eduarbo/filo36/docs/images/branding/flan36-caramel-drop.png

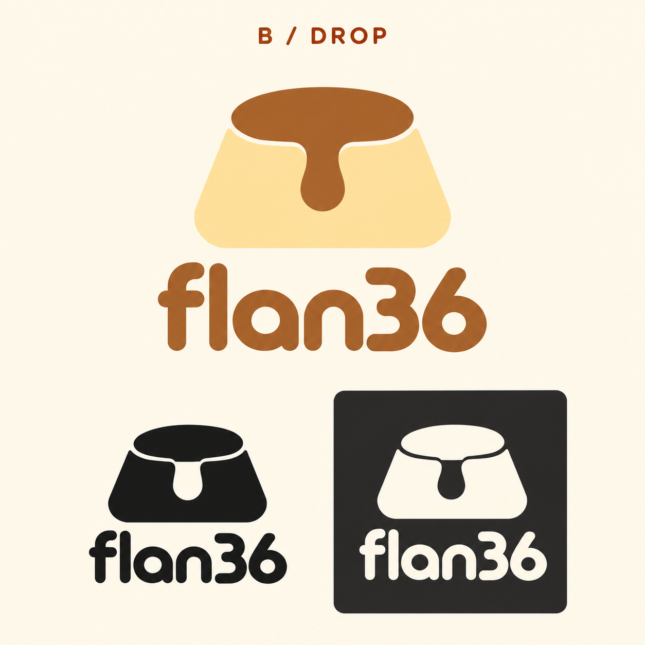
docs/images/branding/flan36-caramel-drop.png
