eduarbo/filo36/docs/images/branding/flan36-caramel-outline.png

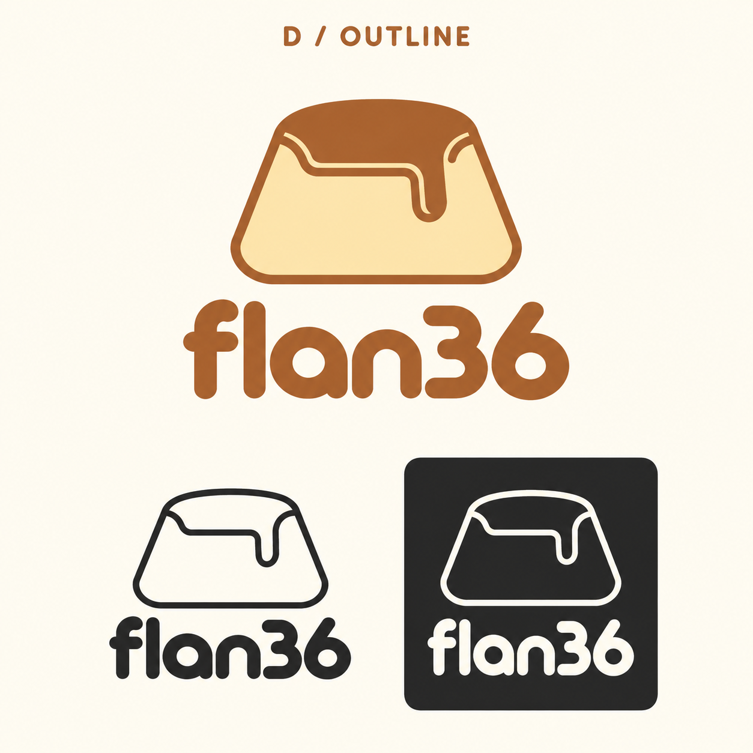
docs/images/branding/flan36-caramel-outline.png
