eduarbo/filo36/docs/images/branding/flan36-caramel-soft.png

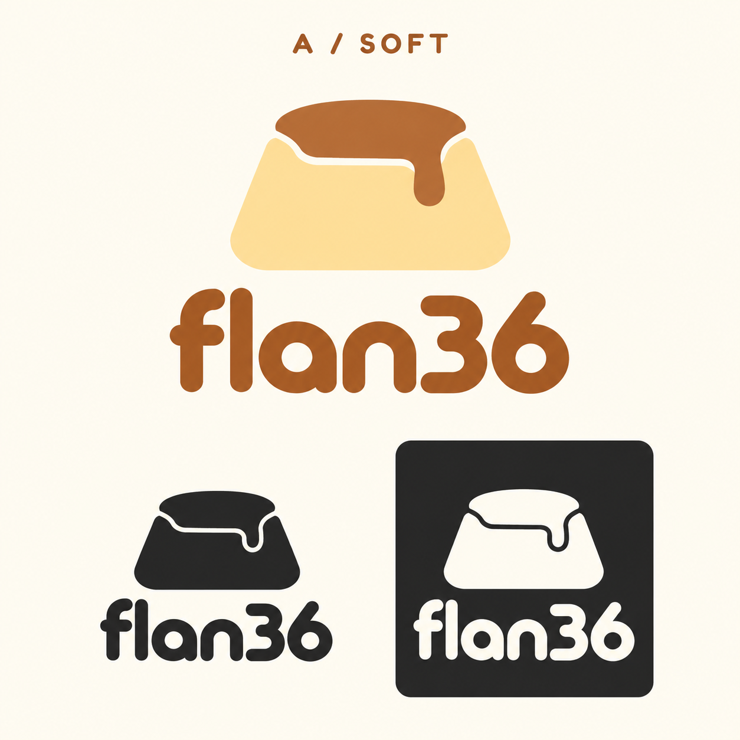
docs/images/branding/flan36-caramel-soft.png
