eduarbo/filo36/docs/images/revE-stack.png

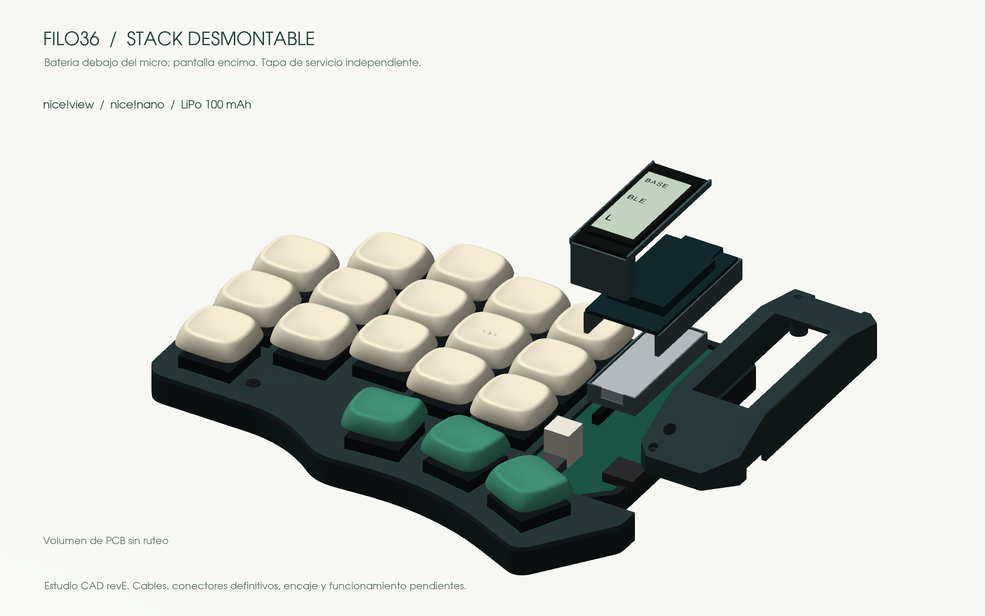
docs/images/revE-stack.png
