eduarbo/filo36/docs/images/revE-top.png

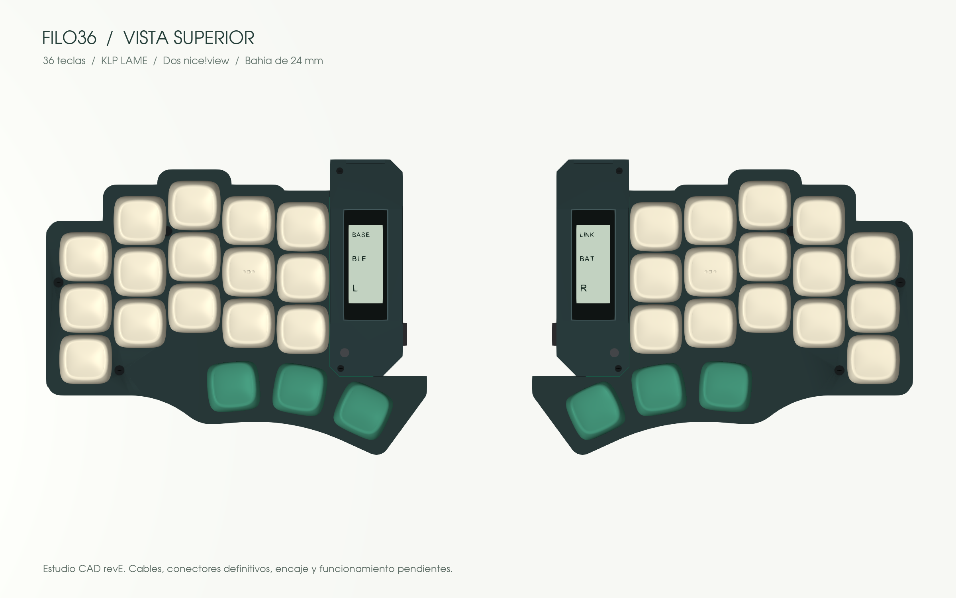
docs/images/revE-top.png
