eduarbo/filo36/docs/images/revF-stack.png

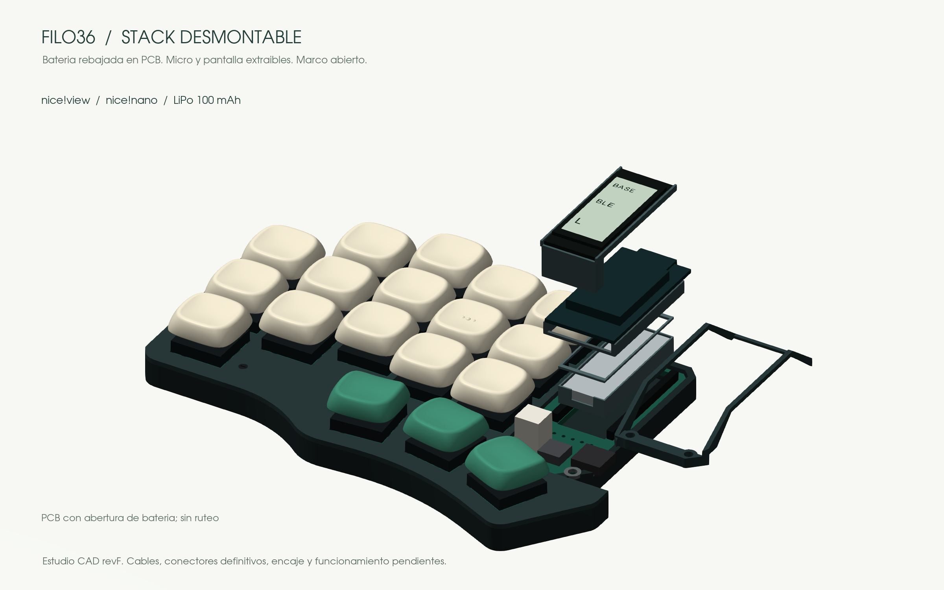
docs/images/revF-stack.png
