eduarbo/filo36/docs/images/revG-frames.png

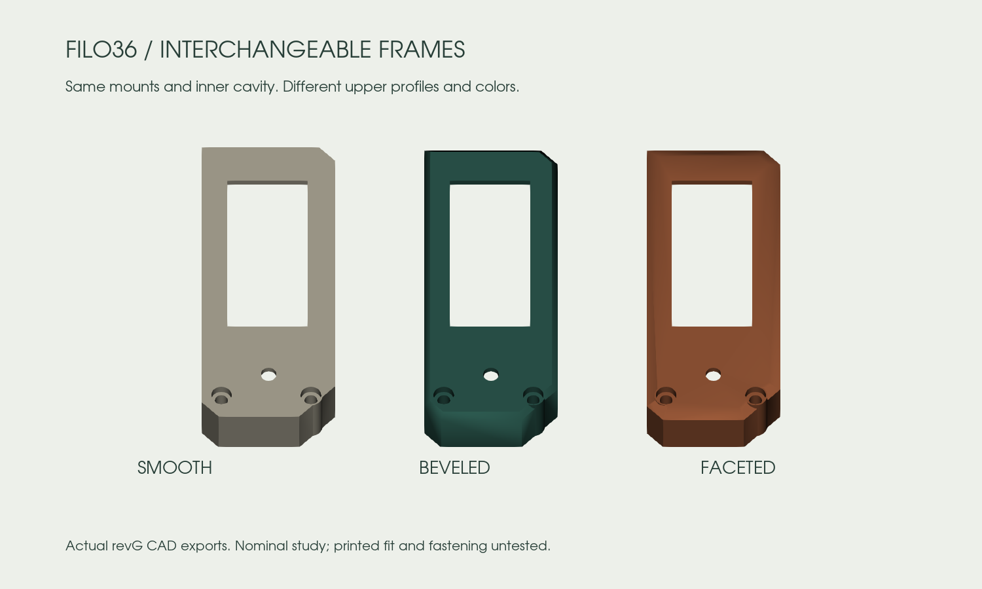
docs/images/revG-frames.png
