eduarbo/filo36/docs/images/revH-detail.png

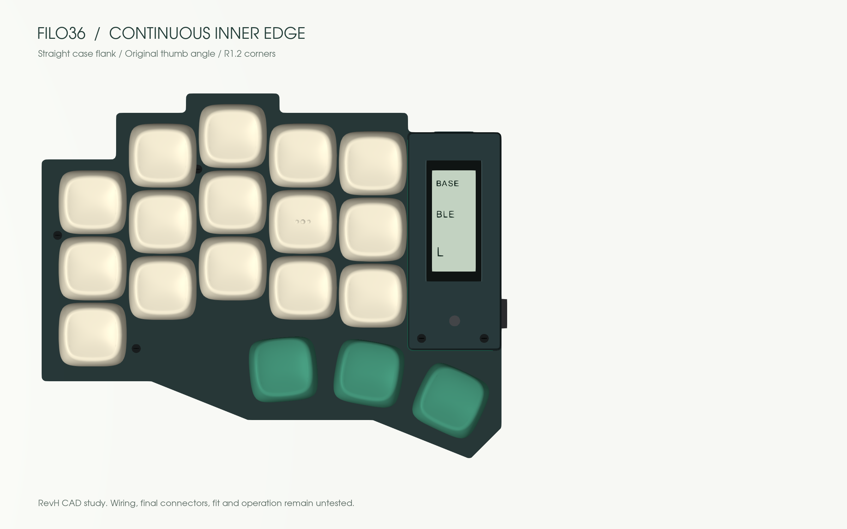
docs/images/revH-detail.png
