eduarbo/filo36/docs/images/revH-frames.png

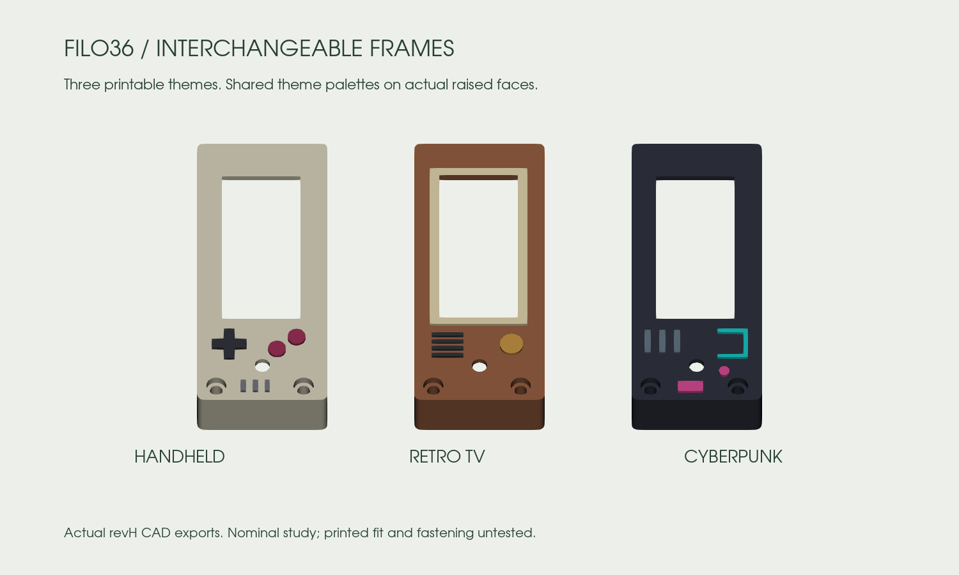
docs/images/revH-frames.png
