eduarbo/filo36/docs/images/viewer-explorer.png

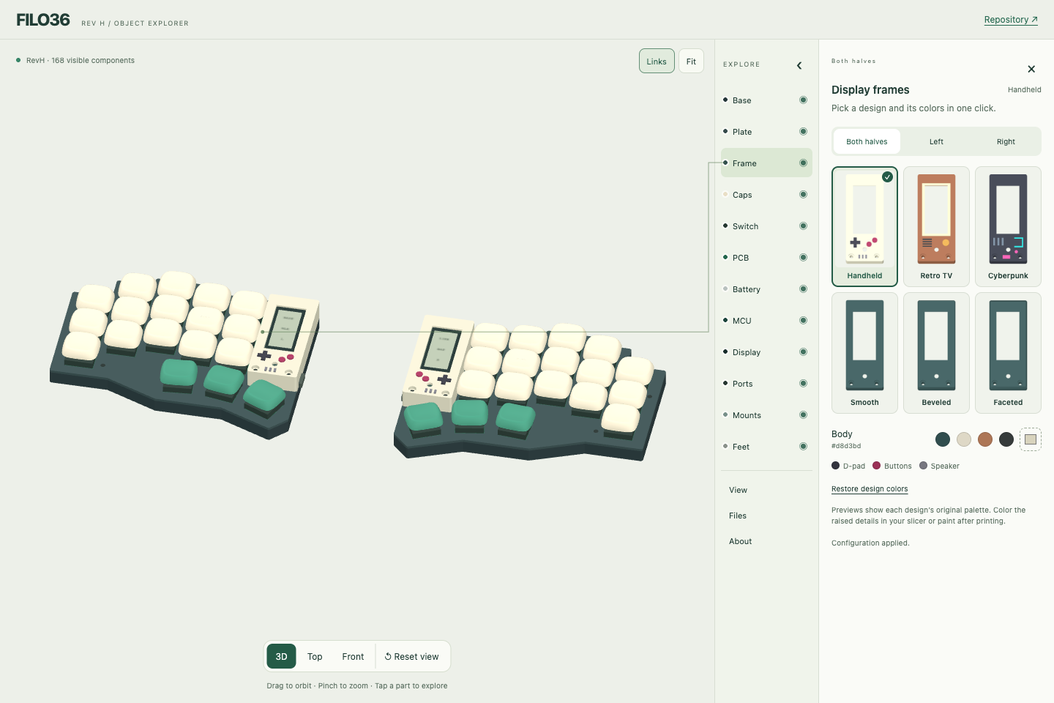
docs/images/viewer-explorer.png
