eduarbo/filo36/components/sources/SW_Hotswap_Kailh_Choc_v1.FCStd

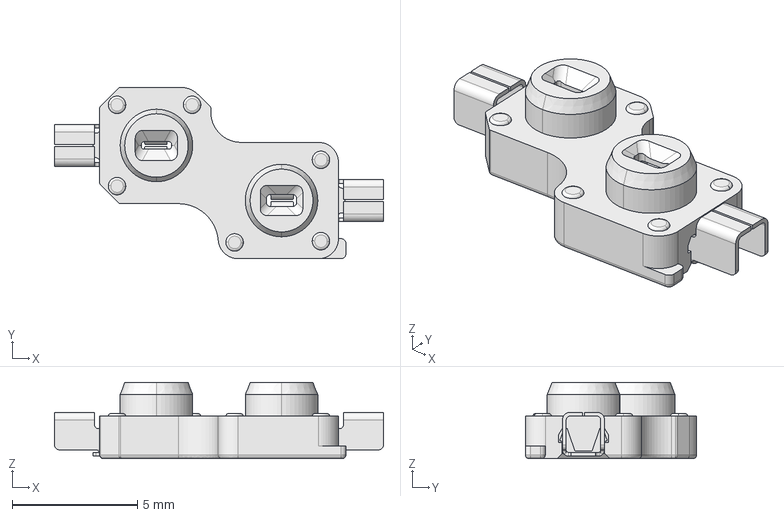
[picture p45: CAD file, 2026-09-22]
components/sources/SW_Hotswap_Kailh_Choc_v1.FCStd
13.2 x 6.85 x 3.05 mm
