eduarbo/filo36/mechanical/revI/left-case-solid-base.step

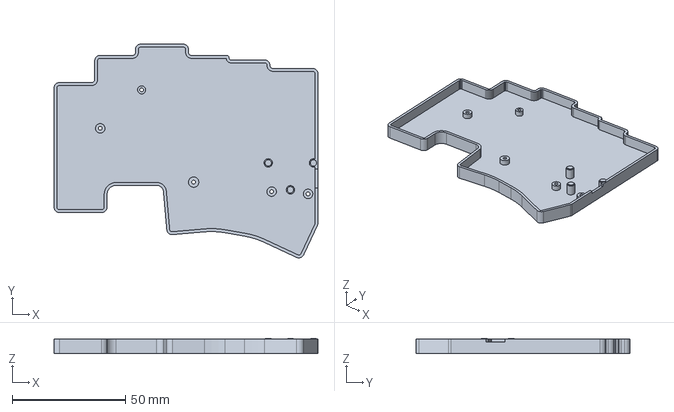
[picture p47: CAD file, 2026-09-23]
mechanical/revI/left-case-solid-base.step
116.8 x 94.6 x 6.60 mm
