eduarbo/filo36/keycaps/variants/Choc_Stem_Choc_Size_1.5U_Normal.stl

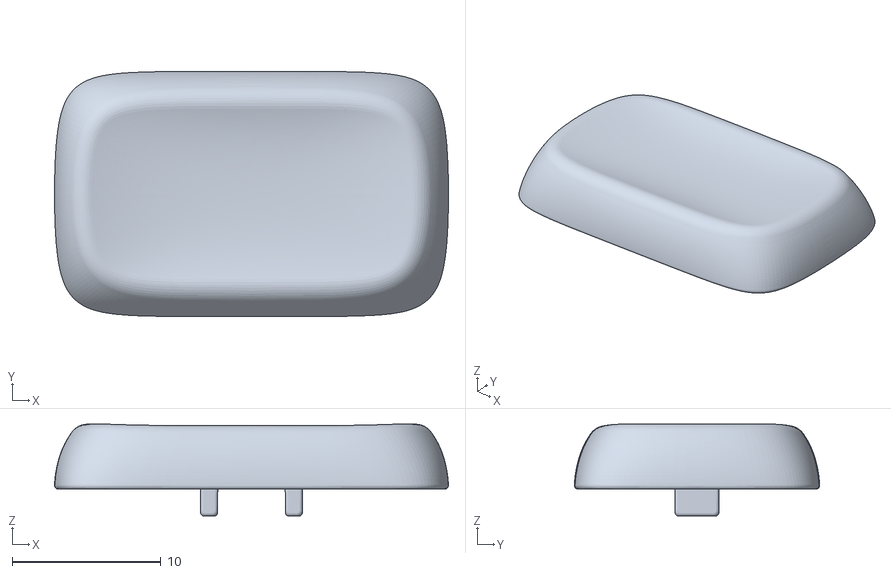
[picture p49: CAD file, 2026-09-22]
keycaps/variants/Choc_Stem_Choc_Size_1.5U_Normal.stl
26.5 x 16.5 x 6.18
