eduarbo/filo36/mechanical/revI/left-mcu-riser.step

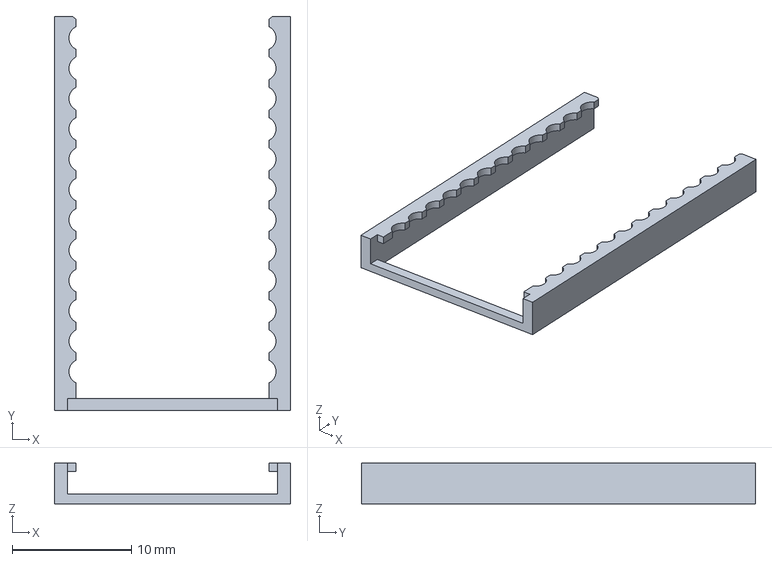
[picture p50: CAD file, 2026-09-23]
mechanical/revI/left-mcu-riser.step
19.8 x 33.0 x 3.40 mm
