eduarbo/filo36/keycaps/variants/Choc_Stem_Choc_Size_Saddle_Tilted_90deg.stl

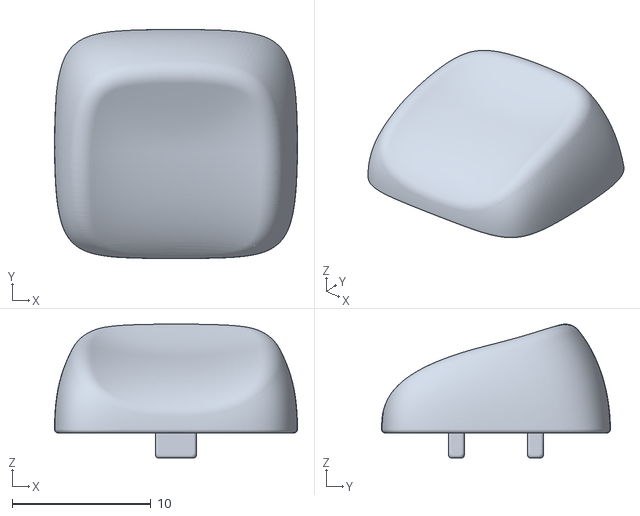
[picture p51: CAD file, 2026-09-22]
keycaps/variants/Choc_Stem_Choc_Size_Saddle_Tilted_90deg.stl
17.5 x 16.5 x 9.64
