eduarbo/filo36/mechanical/revI/left-reset-visual-1.stl

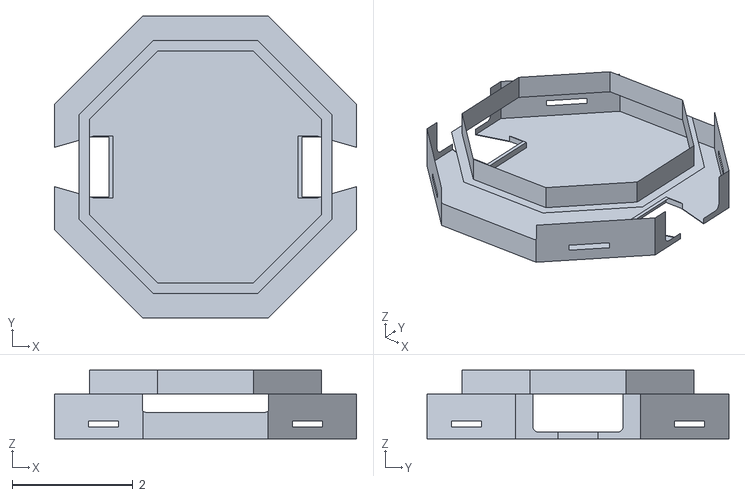
[picture p52: CAD file, 2026-09-23]
mechanical/revI/left-reset-visual-1.stl
5.01 x 5.01 x 1.14
