eduarbo/filo36/mechanical/revI/left-case-terrace-plate.step

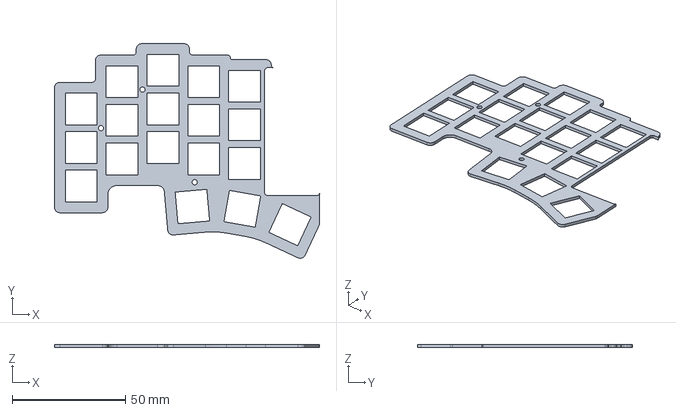
[picture p54: CAD file, 2026-09-23]
mechanical/revI/left-case-terrace-plate.step
116.8 x 94.6 x 1.30 mm
