eduarbo/filo36/mechanical/revI/right-case-rim-plate.step

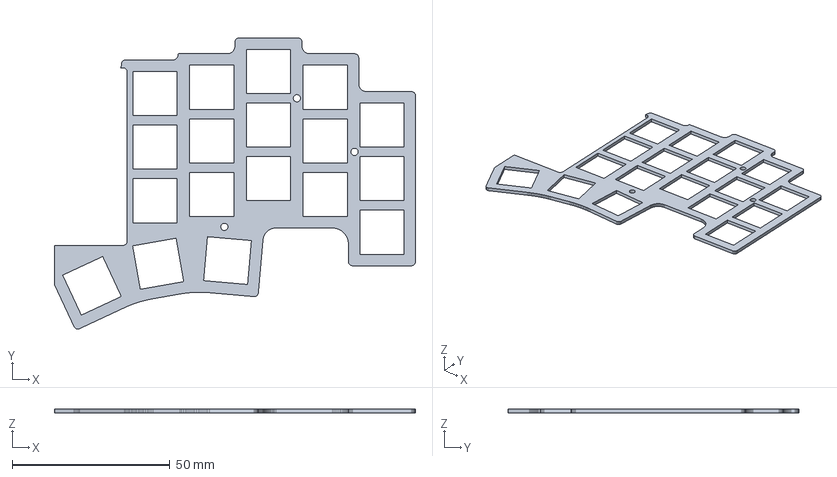
[picture p55: CAD file, 2026-09-23]
mechanical/revI/right-case-rim-plate.step
114.6 x 92.4 x 1.30 mm
