eduarbo/filo36/mechanical/revI/right-display-sled.step

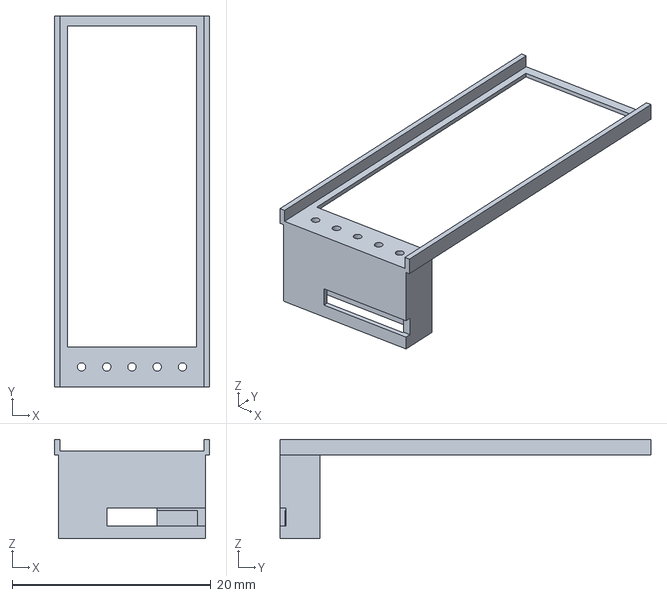
[picture p56: CAD file, 2026-09-23]
mechanical/revI/right-display-sled.step
15.6 x 37.3 x 10.0 mm
