eduarbo/filo36/mechanical/revI/left-cradle.step

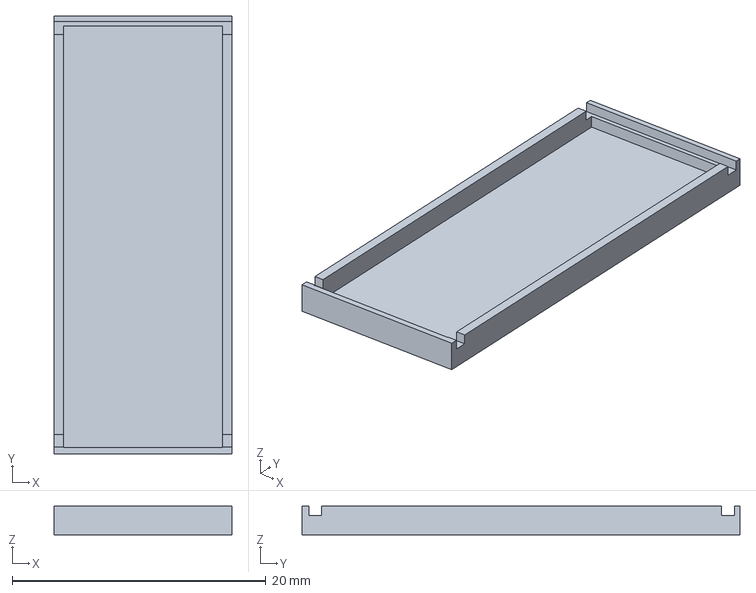
[picture p57: CAD file, 2026-09-23]
mechanical/revI/left-cradle.step
14.0 x 34.5 x 2.25 mm
