eduarbo/filo36/keycaps/variants/Choc_Stem_Choc_Size_1.5U_Saddle_V.stl

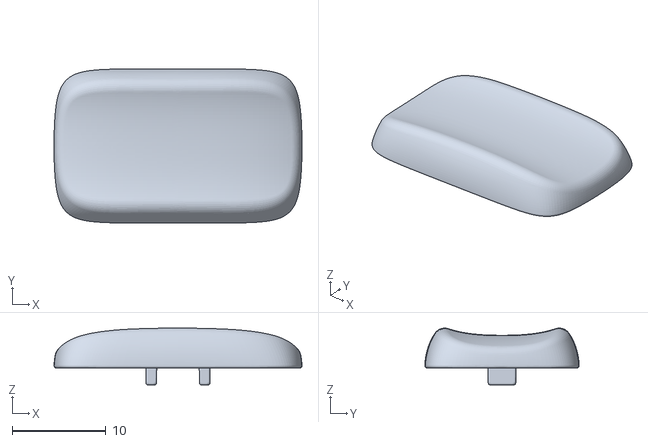
[picture p59: CAD file, 2026-09-22]
keycaps/variants/Choc_Stem_Choc_Size_1.5U_Saddle_V.stl
26.5 x 16.5 x 6.07
