eduarbo/filo36/mechanical/revI/left-case-rim-base.step

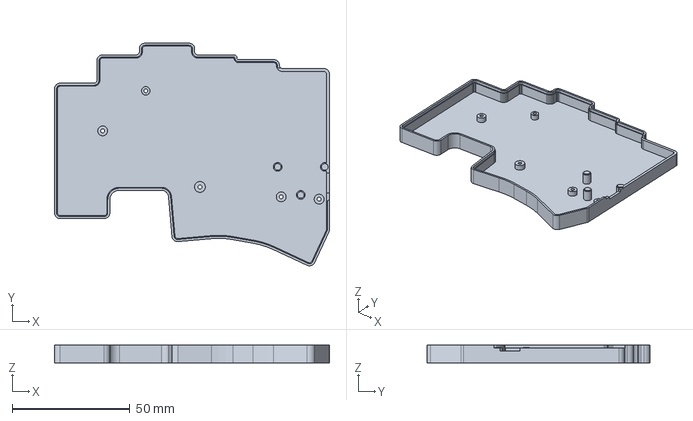
[picture p60: CAD file, 2026-09-23]
mechanical/revI/left-case-rim-base.step
116.8 x 94.6 x 7.60 mm
