eduarbo/filo36/keycaps/variants/Choc_Stem_MX_Size_Thumb.stl

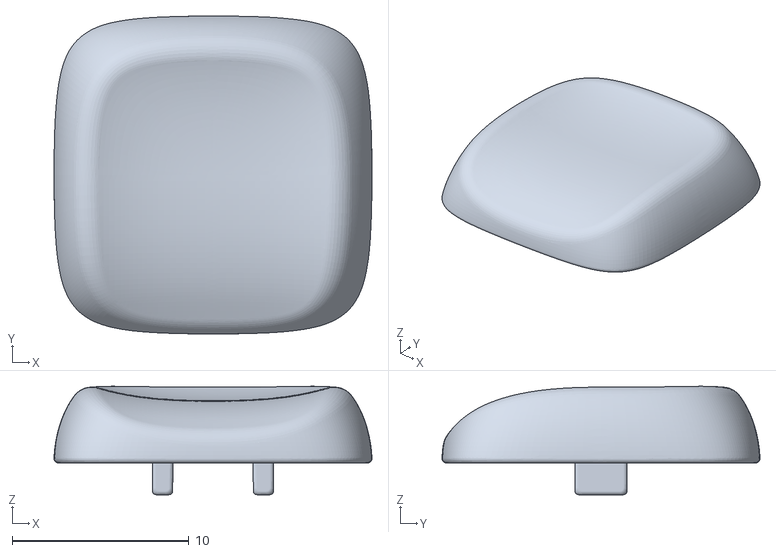
[picture p61: CAD file, 2026-09-22]
keycaps/variants/Choc_Stem_MX_Size_Thumb.stl
18.0 x 18.0 x 6.14
