eduarbo/filo36/mechanical/revI/left-reset-visual-2.stl

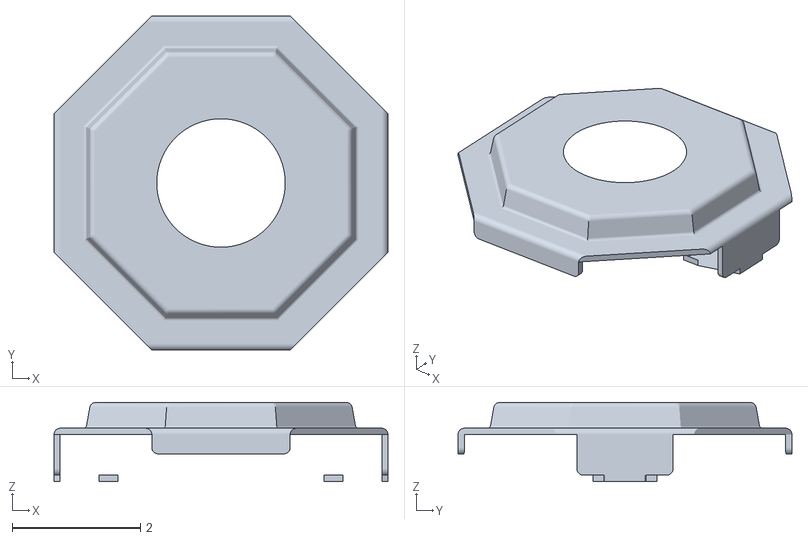
[picture p63: CAD file, 2026-09-23]
mechanical/revI/left-reset-visual-2.stl
5.20 x 5.20 x 1.23
