eduarbo/filo36/mechanical/revI/left-frame-cyberpunk.step

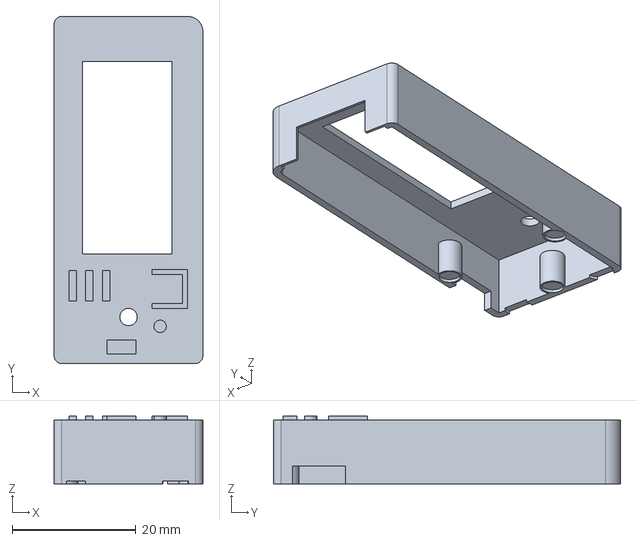
[picture p64: CAD file, 2026-09-23]
mechanical/revI/left-frame-cyberpunk.step
24.0 x 56.0 x 10.9 mm
