eduarbo/filo36/keycaps/variants/Choc_Stem_MX_Size_1.5U_Saddle_V.stl

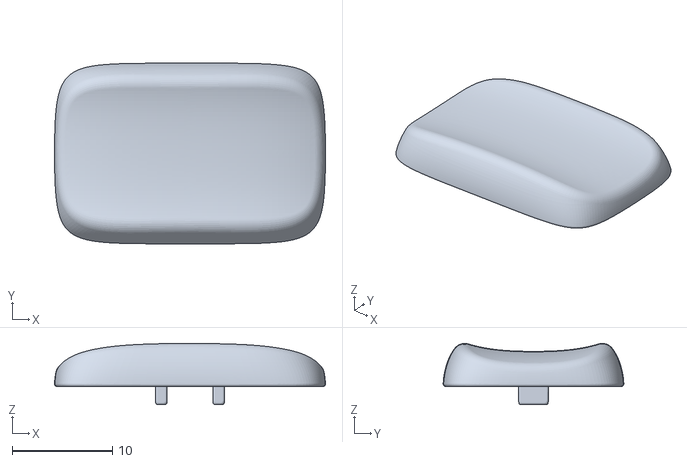
[picture p66: CAD file, 2026-09-22]
keycaps/variants/Choc_Stem_MX_Size_1.5U_Saddle_V.stl
27.0 x 18.0 x 6.09
