eduarbo/filo36/mechanical/revI/left-reset-visual-3.stl

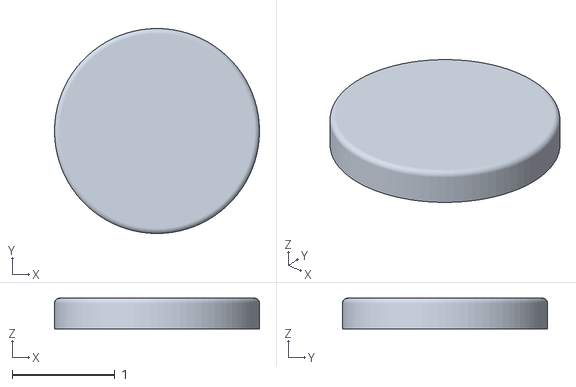
[picture p67: CAD file, 2026-09-23]
mechanical/revI/left-reset-visual-3.stl
2.00 x 2.00 x 0.3
