eduarbo/filo36/keycaps/variants/Choc_Stem_MX_Size_1.5U_Saddle_H.stl

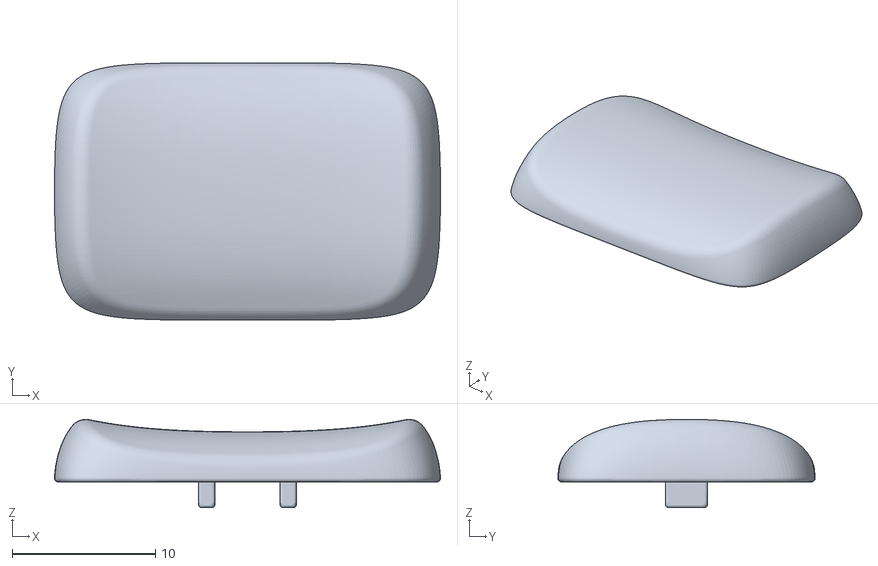
[picture p68: CAD file, 2026-09-22]
keycaps/variants/Choc_Stem_MX_Size_1.5U_Saddle_H.stl
27.0 x 18.0 x 6.17
