eduarbo/filo36/mechanical/revI/right-slider-visual-2.stl

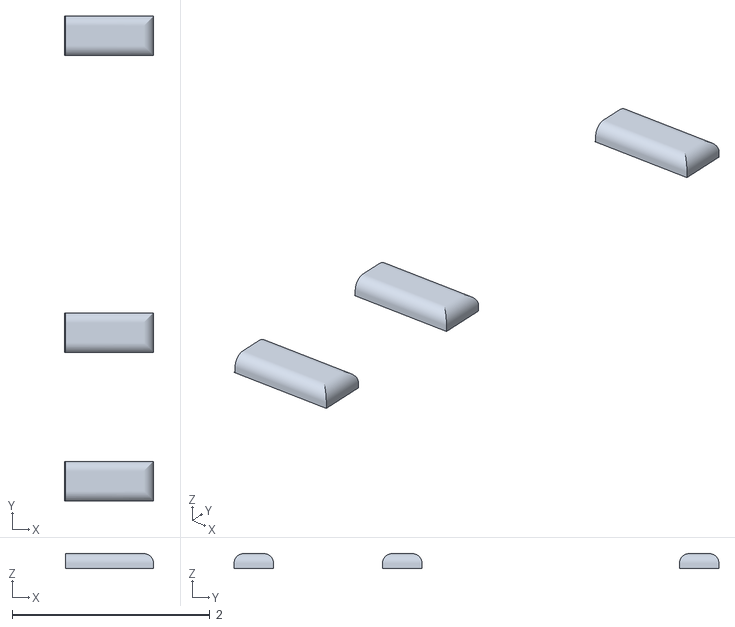
[picture p69: CAD file, 2026-09-23]
mechanical/revI/right-slider-visual-2.stl
0.9 x 4.90 x 0.15
