eduarbo/filo36/mechanical/revI/left-slider-visual-0.stl

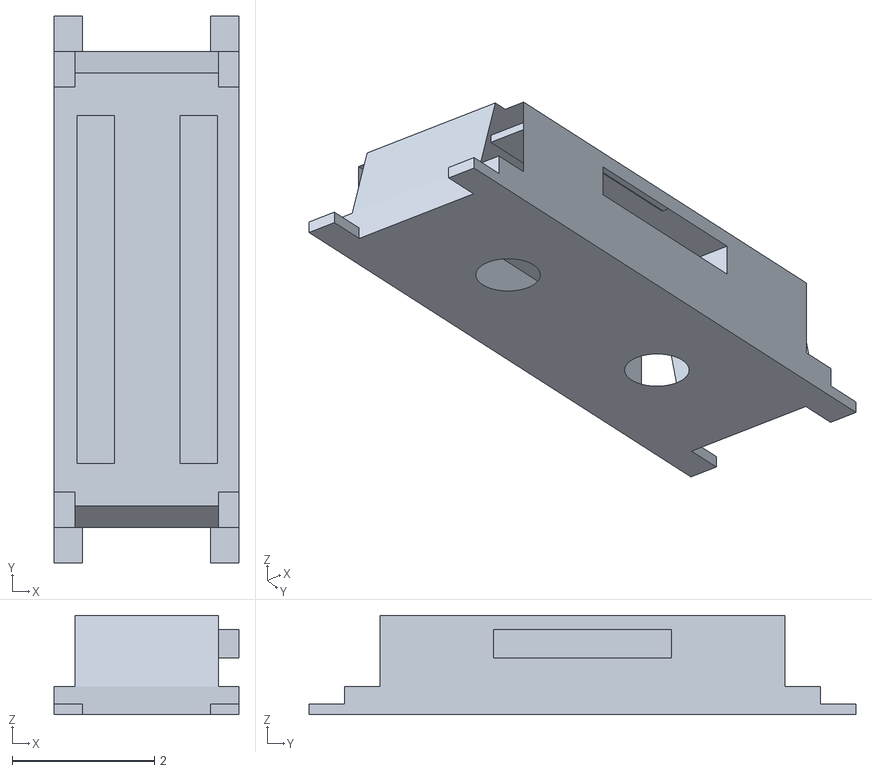
[picture p70: CAD file, 2026-09-23]
mechanical/revI/left-slider-visual-0.stl
2.60 x 7.70 x 1.40
