eduarbo/filo36/mechanical/revI/left-battery-retainer.step

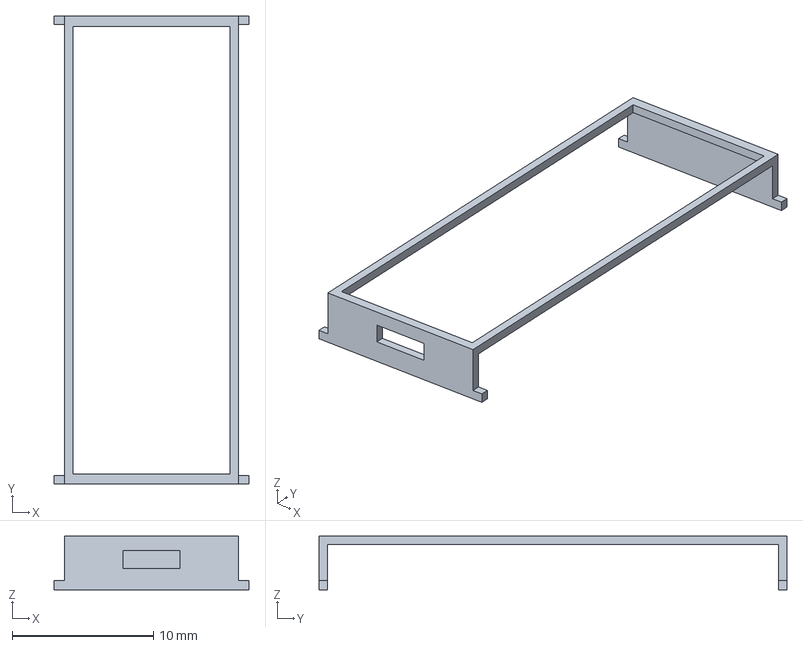
[picture p71: CAD file, 2026-09-23]
mechanical/revI/left-battery-retainer.step
13.8 x 33.1 x 3.80 mm
