eduarbo/filo36/mechanical/revI/coupon-m2-thread.step

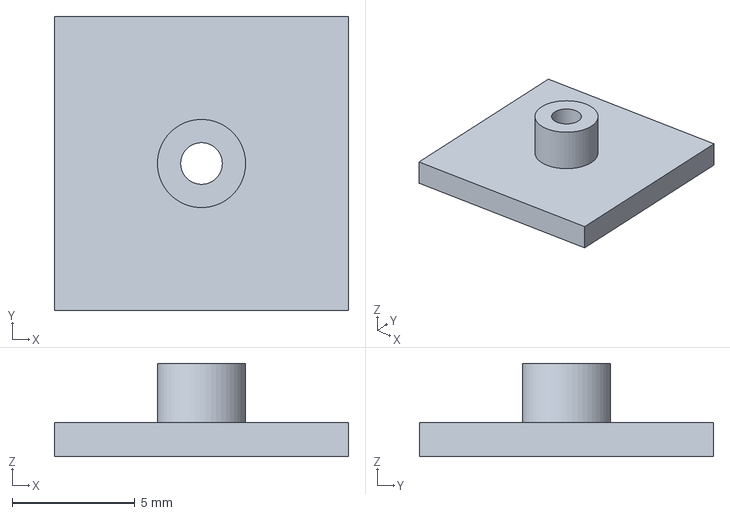
[picture p72: CAD file, 2026-09-23]
mechanical/revI/coupon-m2-thread.step
12.0 x 12.0 x 3.80 mm
