eduarbo/filo36/mechanical/revI/coupon-magnet-base.step

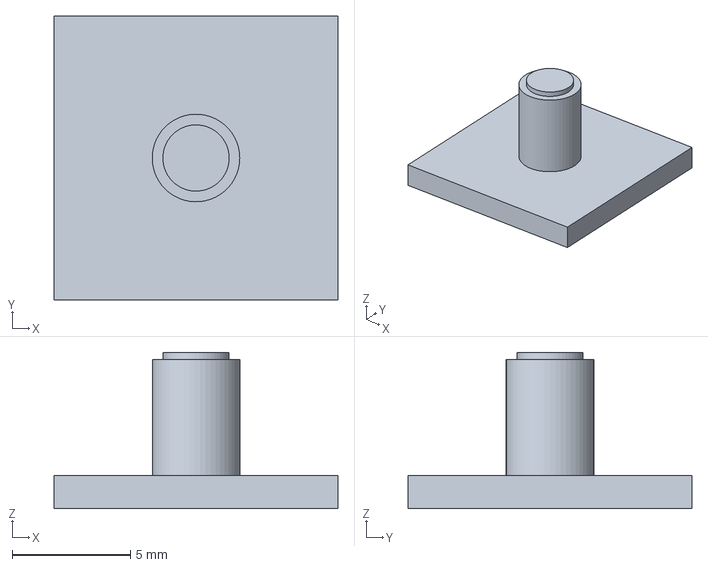
[picture p73: CAD file, 2026-09-23]
mechanical/revI/coupon-magnet-base.step
12.0 x 12.0 x 6.60 mm
