eduarbo/filo36/mechanical/revI/coupon-magnet-frame.step

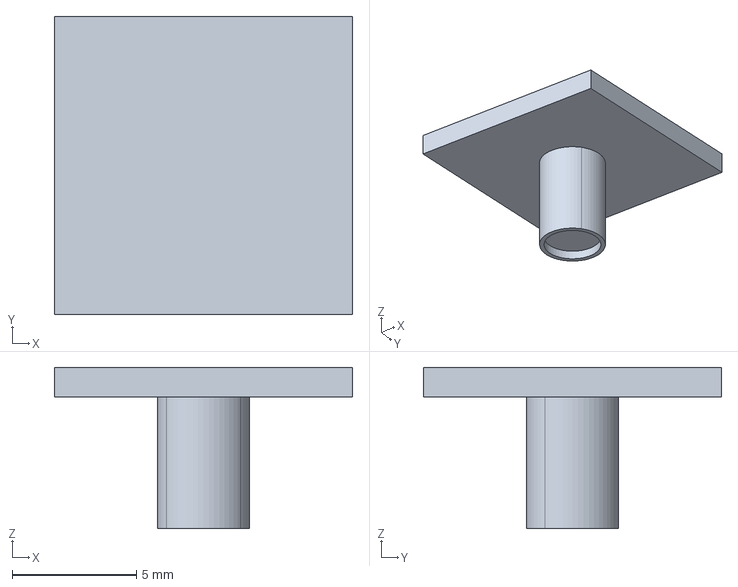
[picture p74: CAD file, 2026-09-23]
mechanical/revI/coupon-magnet-frame.step
12.0 x 12.0 x 6.50 mm
