eduarbo/filo36/mechanical/revI/component-choc-stem-0.stl

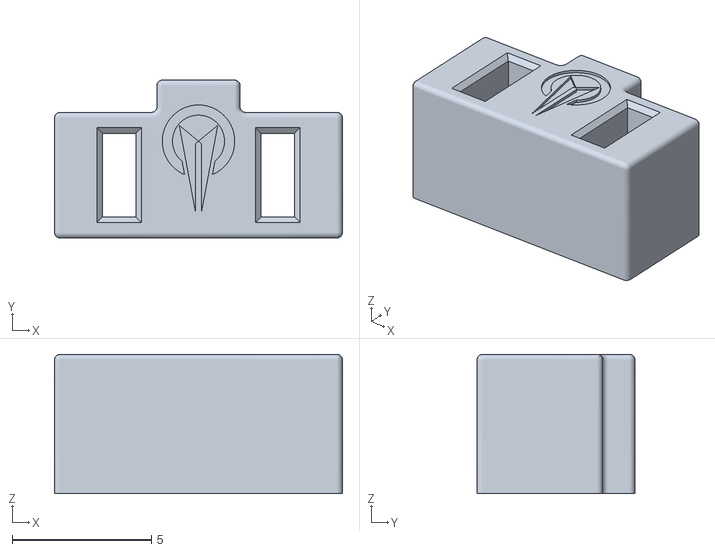
[picture p75: CAD file, 2026-09-22]
mechanical/revI/component-choc-stem-0.stl
10.3 x 5.66 x 5.00
