eduarbo/filo36/mechanical/revI/left-mcu-visual-7.stl

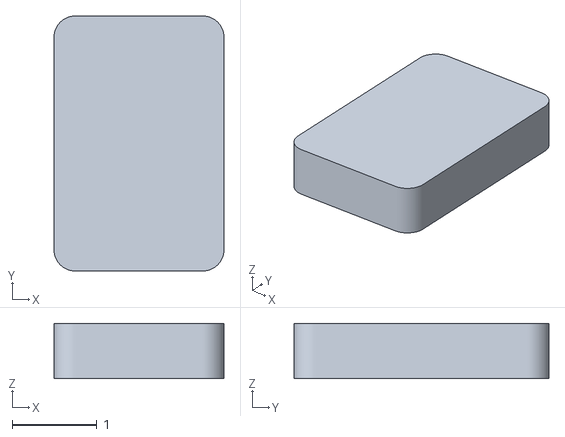
[picture p76: CAD file, 2026-09-22]
mechanical/revI/left-mcu-visual-7.stl
2.00 x 3.00 x 0.65
