eduarbo/filo36/mechanical/revI/left-mcu-visual-0.stl

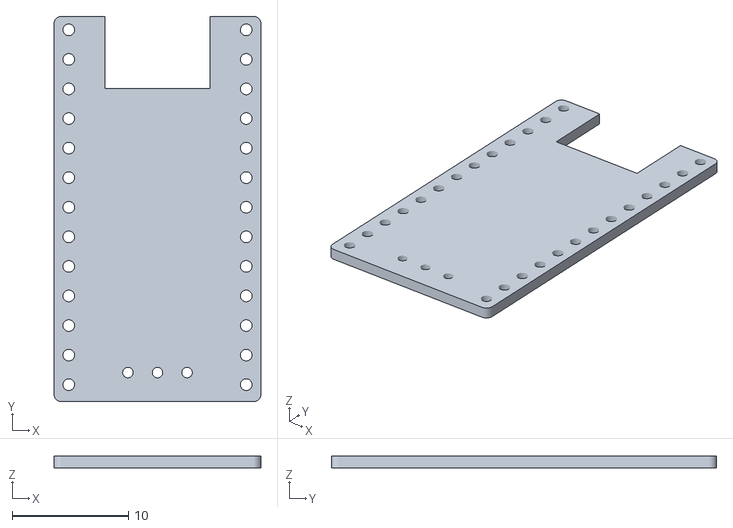
[picture p77: CAD file, 2026-09-22]
mechanical/revI/left-mcu-visual-0.stl
17.8 x 33.1 x 1.00
