eduarbo/filo36/mechanical/revI/left-pcb.stl

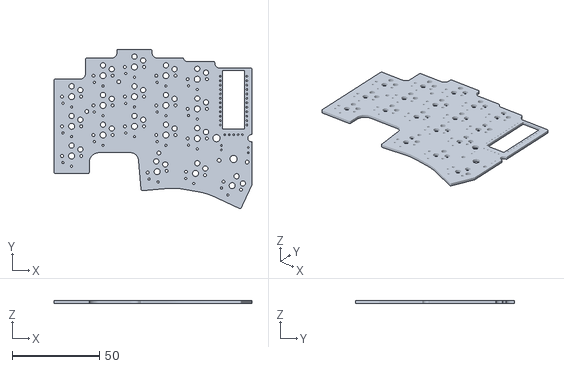
[picture p78: CAD file, 2026-09-22]
mechanical/revI/left-pcb.stl
113.5 x 91.3 x 1.60
