eduarbo/filo36/mechanical/revI/left-mcu-visual-2.stl

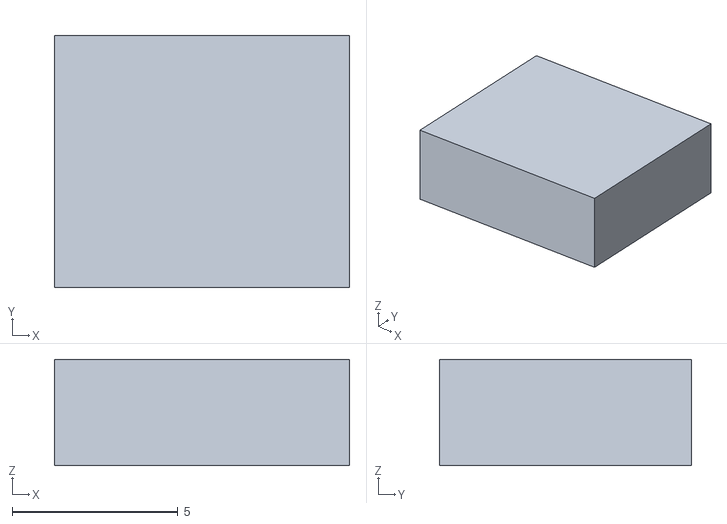
[picture p79: CAD file, 2026-09-22]
mechanical/revI/left-mcu-visual-2.stl
8.90 x 7.60 x 3.20
