eduarbo/filo36/mechanical/revI/right-mcu-visual-4.stl

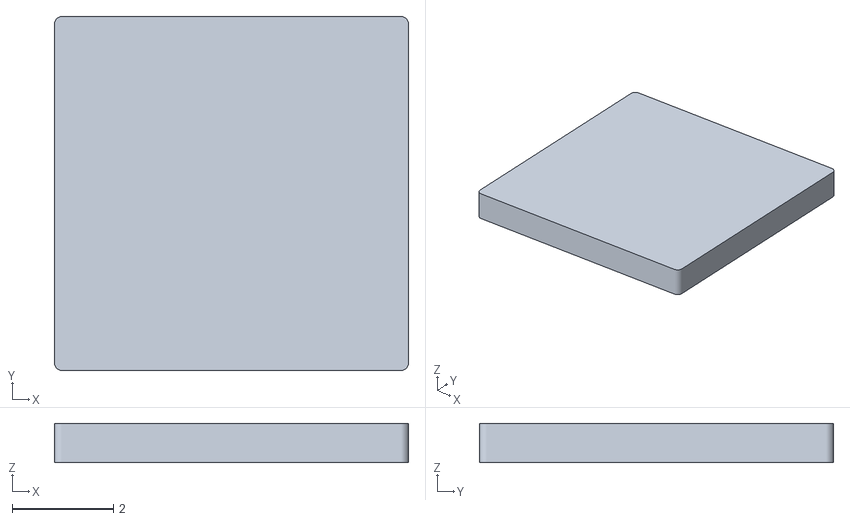
[picture p80: CAD file, 2026-09-22]
mechanical/revI/right-mcu-visual-4.stl
7.00 x 7.00 x 0.78
