eduarbo/filo36/mechanical/revI/left-display-visual-3.stl

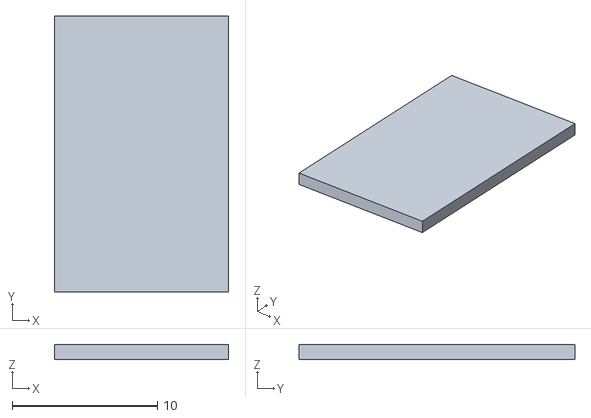
[picture p81: CAD file, 2026-09-22]
mechanical/revI/left-display-visual-3.stl
12.0 x 19.0 x 1.00
