eduarbo/filo36/mechanical/revI/right-mcu-visual-5.stl

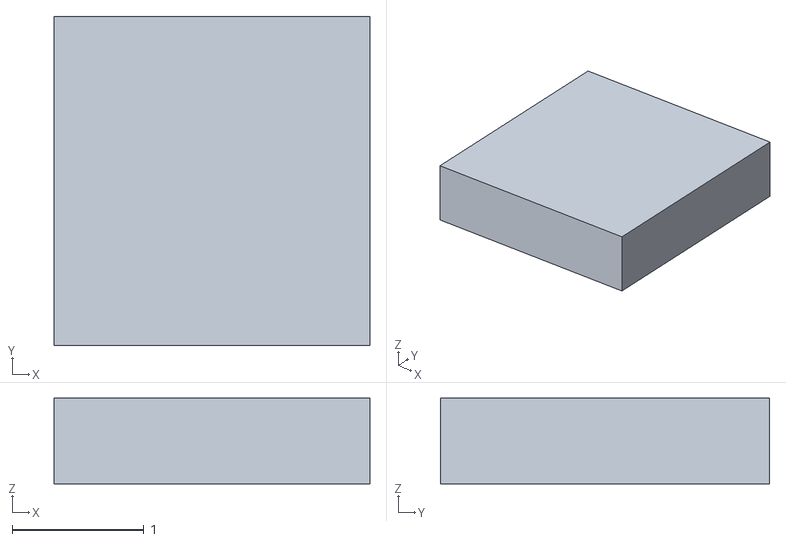
[picture p82: CAD file, 2026-09-22]
mechanical/revI/right-mcu-visual-5.stl
2.40 x 2.50 x 0.65
