eduarbo/filo36/mechanical/revI/left-battery-lead-0.stl

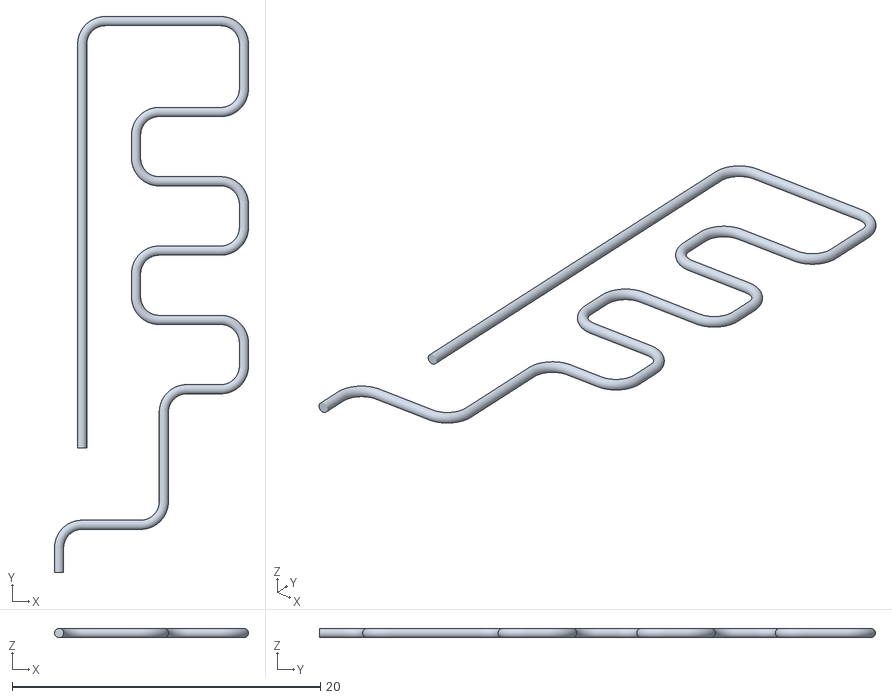
[picture p83: CAD file, 2026-09-22]
mechanical/revI/left-battery-lead-0.stl
12.6 x 36.1 x 0.6
