eduarbo/filo36/mechanical/revI/right-mcu-visual-10.stl

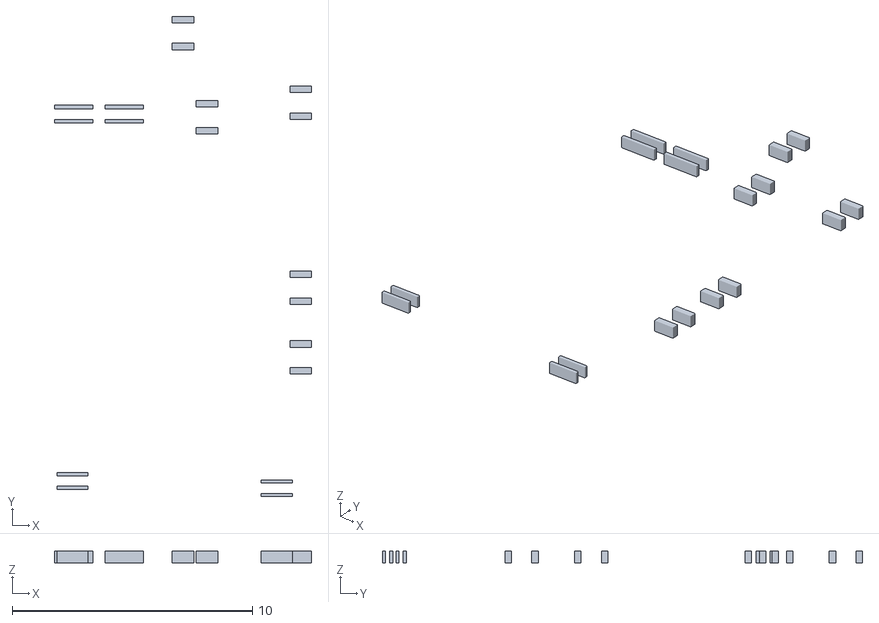
[picture p84: CAD file, 2026-09-22]
mechanical/revI/right-mcu-visual-10.stl
10.7 x 20.0 x 0.48
