eduarbo/filo36/mechanical/revI/left-display-visual-1.stl

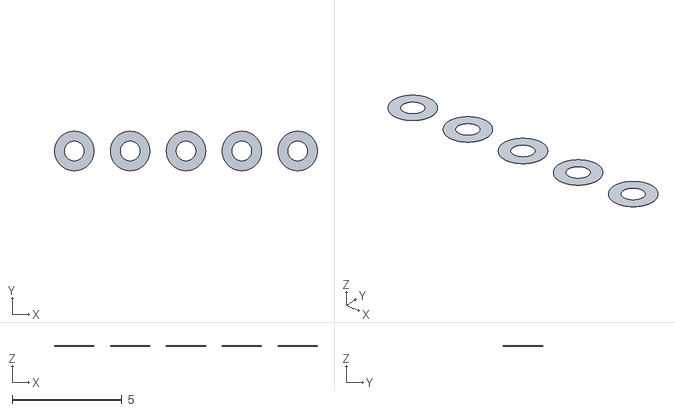
[picture p85: CAD file, 2026-09-22]
mechanical/revI/left-display-visual-1.stl
12.0 x 1.80 x 0.035
