eduarbo/filo36/mechanical/revI/left-mcu-visual-8.stl

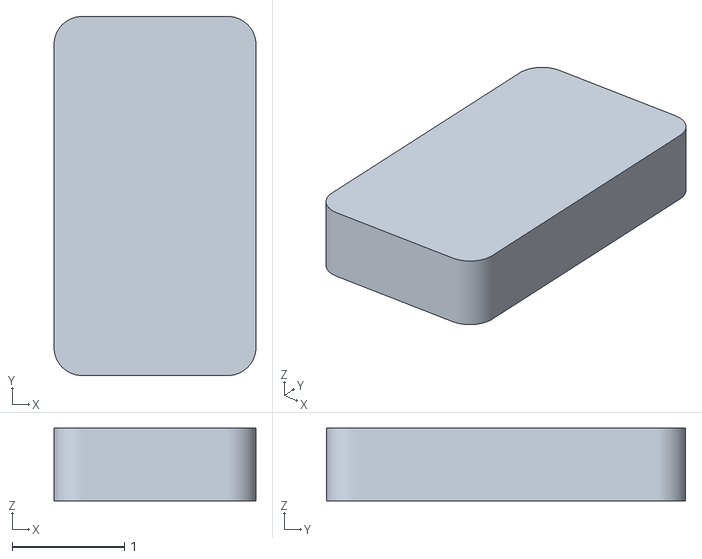
[picture p86: CAD file, 2026-09-22]
mechanical/revI/left-mcu-visual-8.stl
1.80 x 3.20 x 0.65
