eduarbo/filo36/mechanical/revI/right-mcu-visual-1.stl

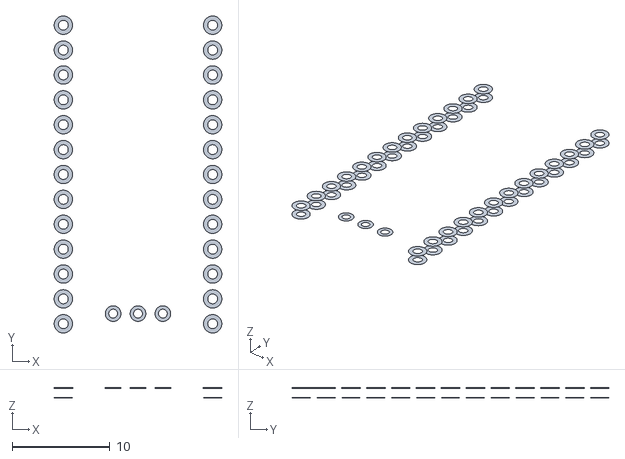
[picture p87: CAD file, 2026-09-22]
mechanical/revI/right-mcu-visual-1.stl
17.1 x 32.4 x 1.07
