eduarbo/filo36/mechanical/revI/left-display-visual-2.stl

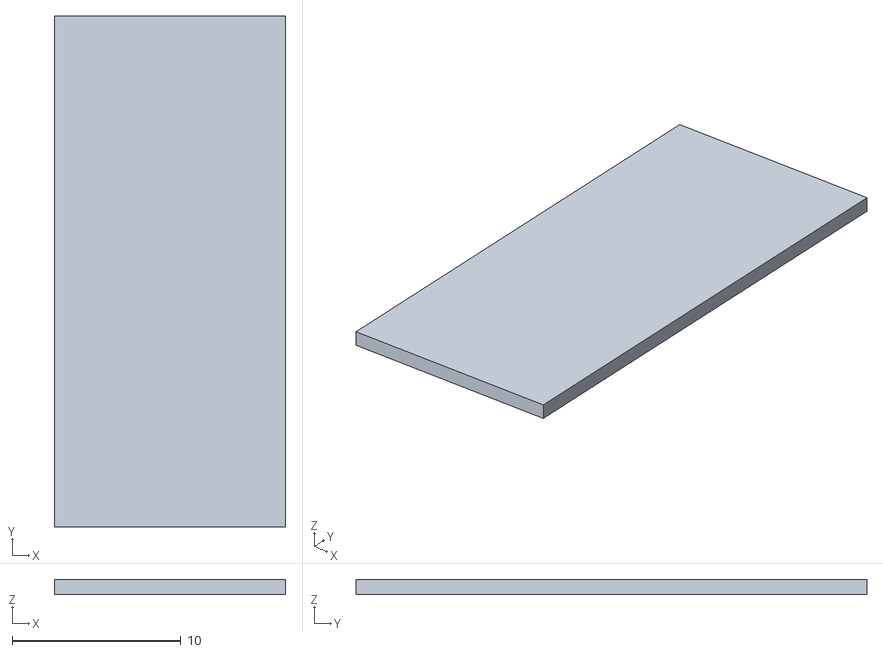
[picture p88: CAD file, 2026-09-22]
mechanical/revI/left-display-visual-2.stl
13.7 x 30.3 x 0.9
