eduarbo/filo36/mechanical/revI/right-mcu-visual-11.stl

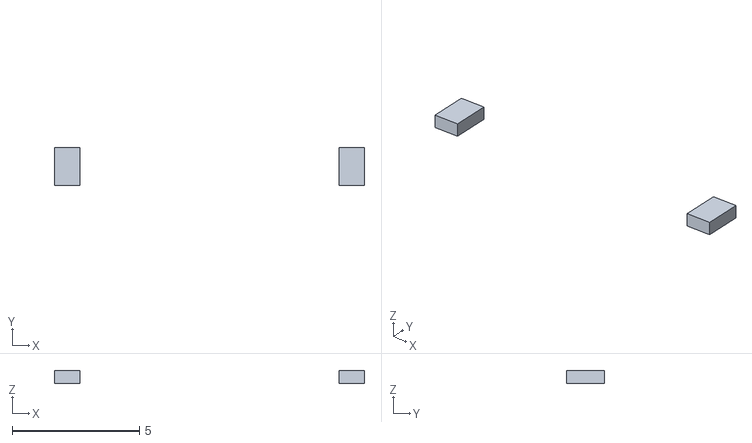
[picture p89: CAD file, 2026-09-22]
mechanical/revI/right-mcu-visual-11.stl
12.2 x 1.50 x 0.5
