eduarbo/filo36/mechanical/revI/left-display-visual-0.stl

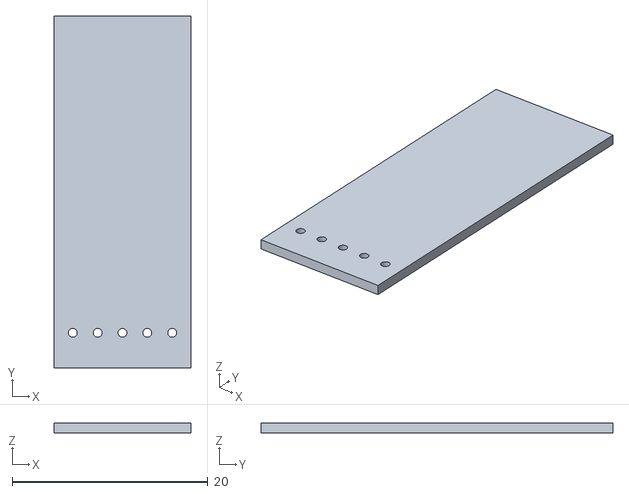
[picture p90: CAD file, 2026-09-22]
mechanical/revI/left-display-visual-0.stl
14.0 x 36.0 x 1.00
