eduarbo/filo36/mechanical/revI/right-mcu-visual-3.stl

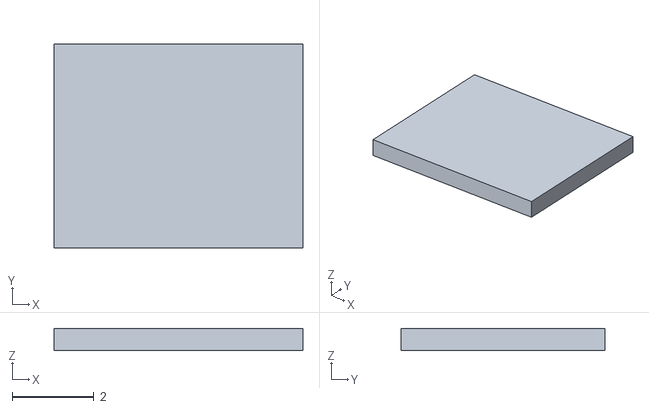
[picture p91: CAD file, 2026-09-22]
mechanical/revI/right-mcu-visual-3.stl
6.10 x 5.00 x 0.55
