eduarbo/filo36/mechanical/revI/left-mcu-visual-9.stl

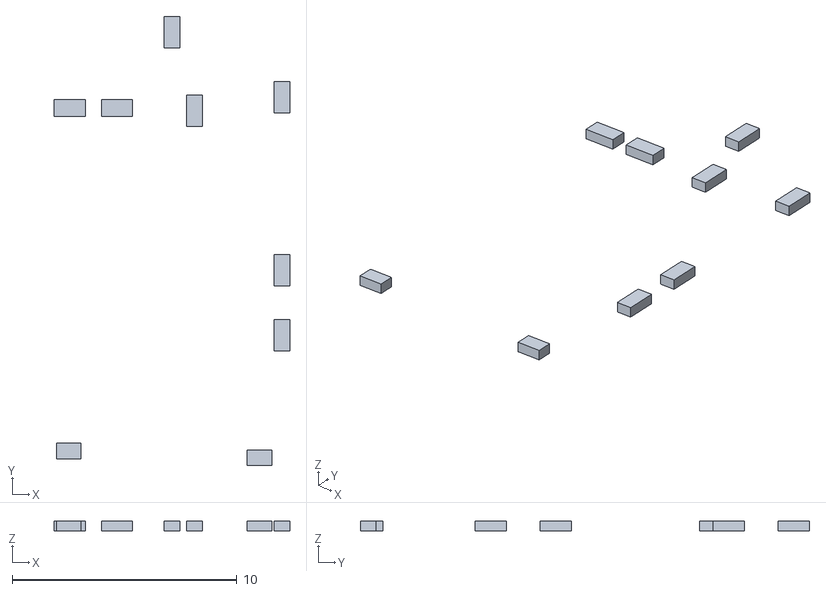
[picture p92: CAD file, 2026-09-22]
mechanical/revI/left-mcu-visual-9.stl
10.5 x 20.0 x 0.45
