eduarbo/filo36/mechanical/revI/component-choc-body-2.stl

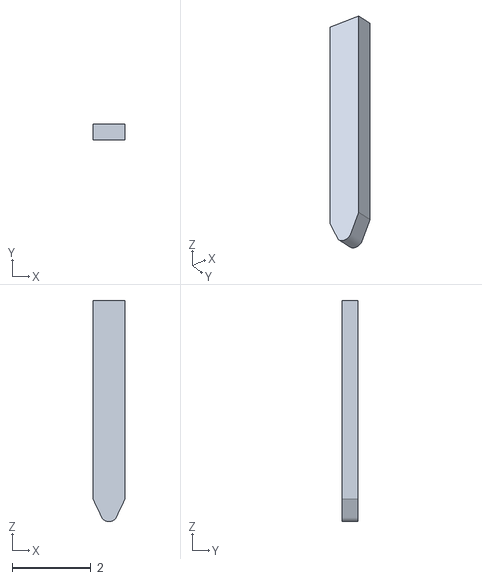
[picture p93: CAD file, 2026-09-22]
mechanical/revI/component-choc-body-2.stl
0.811 x 0.411 x 5.60
